michaelmurf01/CUISLE/Slicer_Images/Pump_Enclosure_Lid.png

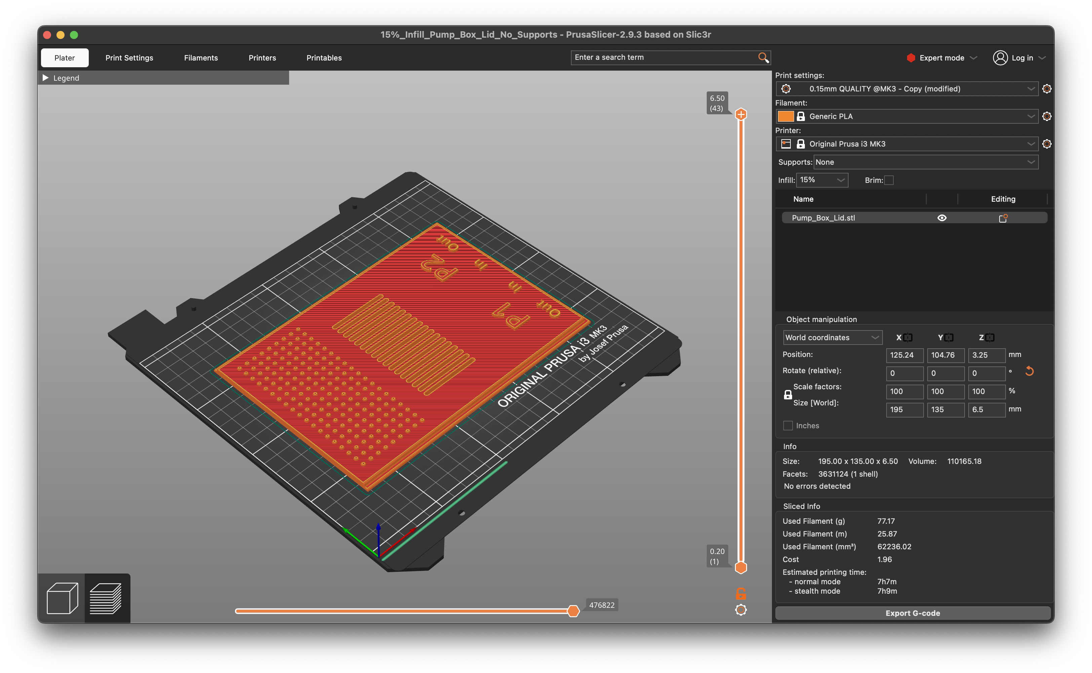
Slicer_Images/Pump_Enclosure_Lid.png
