michaelmurf01/CUISLE/STL_Parts/Pulley_Wheel.stl

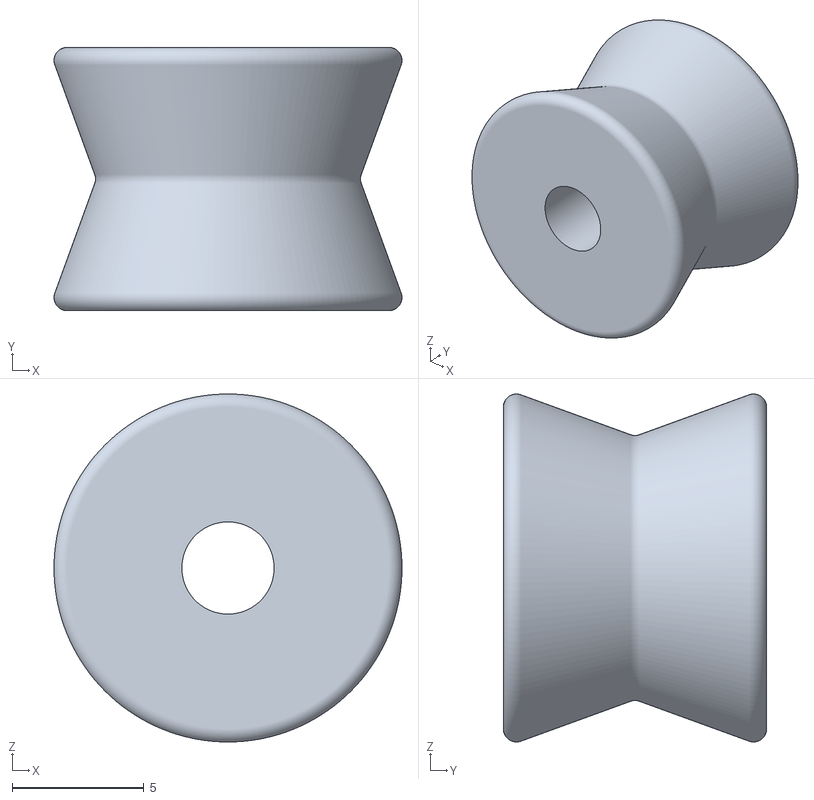
[picture p19: CAD file, 2026-04-17]
STL_Parts/Pulley_Wheel.stl
13.2 x 10.0 x 13.2
