michaelmurf01/CUISLE/STL_Parts/Base.stl

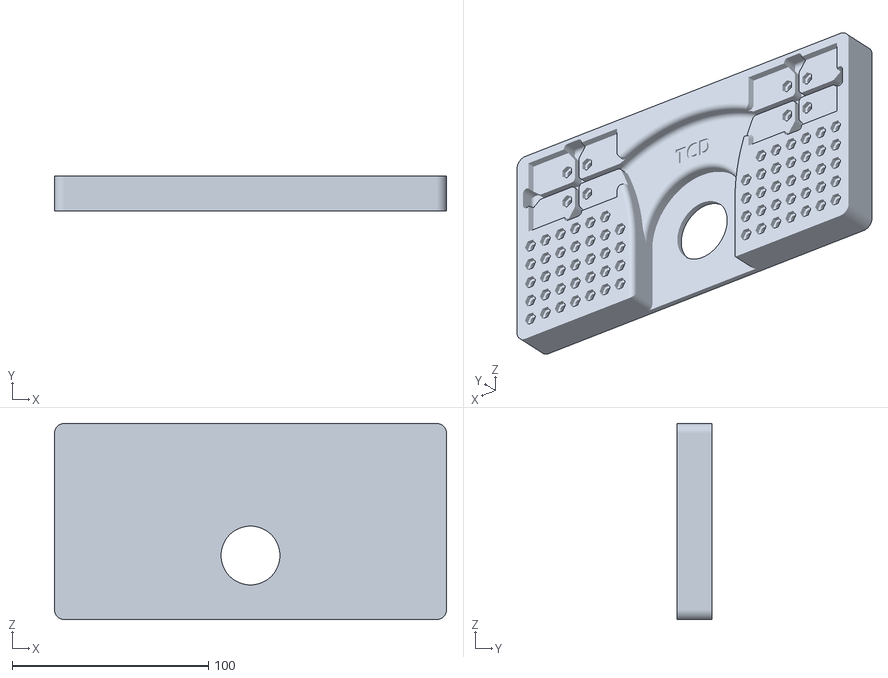
[picture p20: CAD file, 2026-04-17]
STL_Parts/Base.stl
200.0 x 18.0 x 100.0
