michaelmurf01/CUISLE/STL_Parts/MM_Z_Dial_3.0.stl

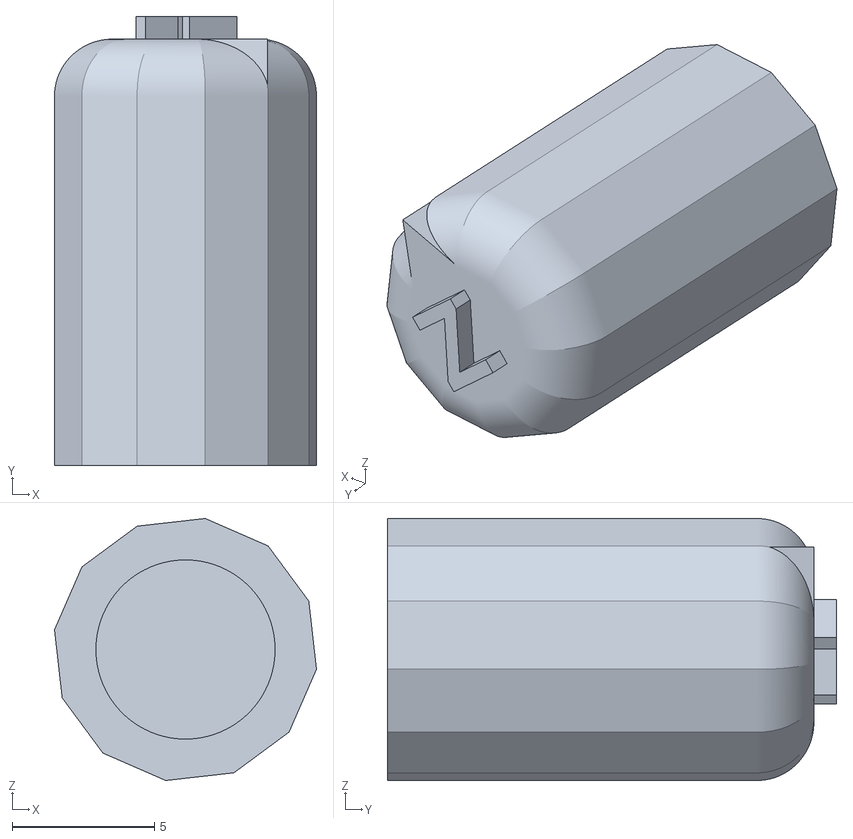
[picture p21: CAD file, 2026-04-17]
STL_Parts/MM_Z_Dial_3.0.stl
9.21 x 15.8 x 9.21
